kyleRhess/MicroMotor/uMotor_0p2/include/encoder.h

#ifndef ENCODER_H_ /* include guard */
#define ENCODER_H_

#include <stdio.h>

#include "stm32f4xx.h"
#include "system.h"

void Encoder_Init(void);
void Encoder_ZInit(void);
uint32_t Encoder_GetCounts(void);
double Encoder_GetAngle(void);
void Encoder_Reset(void);

extern uint32_t sens51[8];
extern uint32_t sens52[8];

#endif /* ENCODER_H_ */
