kyleRhess/MicroMotor/uMotor_0p2/src/adc.c

#include "adc.h"

ADC_HandleTypeDef hadc1;
DMA_HandleTypeDef hdma_adc1;

static uint32_t g_ADCValue1 = 0;
static float g_ADCValue2 	= 0;
static float g_ADCValue3 	= 0;
static float g_ADCValue4 	= 0;
static uint32_t g_ADCBuffer[ADC_BUF_LEN];

static float min_adc =  1.22f;
static float max_adc = 3.4f;
static float adcBias = 0;
static int adcBiasCount = 0;

void ADC_Init(void)
{
	ADC_ChannelConfTypeDef sConfig 		= {0};

	hadc1.Instance 						= ADC1;
	hadc1.Init.ClockPrescaler 			= ADC_CLOCK_SYNC_PCLK_DIV2;
	hadc1.Init.Resolution 				= ADC_RESOLUTION_12B;
	hadc1.Init.ScanConvMode 			= ENABLE;
	hadc1.Init.ContinuousConvMode 		= DISABLE;
	hadc1.Init.DiscontinuousConvMode 	= DISABLE;
	hadc1.Init.ExternalTrigConvEdge 	= ADC_EXTERNALTRIGCONVEDGE_NONE;
	hadc1.Init.ExternalTrigConv 		= ADC_SOFTWARE_START;
	hadc1.Init.DataAlign 				= ADC_DATAALIGN_RIGHT;
	hadc1.Init.NbrOfConversion 			= 4;
	hadc1.Init.DMAContinuousRequests 	= ENABLE;
	hadc1.Init.EOCSelection 			= ADC_EOC_SINGLE_CONV;

	if (HAL_ADC_Init(&hadc1) != HAL_OK)
	{
		Error_Handler();
	}

	sConfig.Channel 		= ADC_CHANNEL_2;
	sConfig.Rank 			= 1;
	sConfig.SamplingTime 	= ADC_SAMPLETIME_3CYCLES;
	if (HAL_ADC_ConfigChannel(&hadc1, &sConfig) != HAL_OK)
	{
		Error_Handler();
	}

	sConfig.Channel 		= ADC_CHANNEL_3;
	sConfig.Rank 			= 2;
	if (HAL_ADC_ConfigChannel(&hadc1, &sConfig) != HAL_OK)
	{
		Error_Handler();
	}

	sConfig.Channel 		= ADC_CHANNEL_15;
	sConfig.Rank 			= 3;
	if (HAL_ADC_ConfigChannel(&hadc1, &sConfig) != HAL_OK)
	{
		Error_Handler();
	}

	sConfig.Channel 		= ADC_CHANNEL_0;
	sConfig.Rank 			= 4;
	if (HAL_ADC_ConfigChannel(&hadc1, &sConfig) != HAL_OK)
	{
		Error_Handler();
	}

	HAL_ADC_Start_DMA(&hadc1, (uint32_t *)&g_ADCBuffer, ADC_BUF_LEN);
}

void HAL_ADC_ConvCpltCallback(ADC_HandleTypeDef* hadc)
{
//#define FILT_K		0.90f
#ifdef FILT_K
#define FILT_K_1	(1 - FILT_K)
	// Initial state needs to be set
	if(g_ADCValue1 == 0 && g_ADCValue2 == 0 && g_ADCValue3 == 0)
	{
		g_ADCValue1 	= g_ADCBuffer[2];
		g_ADCValue2 	= (float)g_ADCBuffer[0];
		g_ADCValue3 	= (float)g_ADCBuffer[1];
		g_ADCValue4 	= (float)g_ADCBuffer[3];
	}
	else
	{
		g_ADCValue1 	= g_ADCBuffer[2];
		g_ADCValue2 	= g_ADCValue2*FILT_K_1 + ((float)g_ADCBuffer[0])*FILT_K;
		g_ADCValue3 	= g_ADCValue3*FILT_K_1 + ((float)g_ADCBuffer[1])*FILT_K;
		g_ADCValue4 	= (float)g_ADCBuffer[3];
	}
#else
	g_ADCValue1 	= (float)g_ADCBuffer[2];
	g_ADCValue2 	= (float)g_ADCBuffer[0];
	g_ADCValue3 	= (float)g_ADCBuffer[1];
	g_ADCValue4 	= (float)g_ADCBuffer[3];
#endif

	m_fSupplyVolt 	= ((float)g_ADCValue1 * ADC_SCALE) / ADC_SUPPLY_DIV;
	m_fThrotVolt	= ((float)g_ADCValue4 * ADC_SCALE) / 0.5f;

	// Take out the throttle bias
	if(adcBiasCount == 9999)
		m_fThrotVolt -= adcBias;

	m_fCurrentA 	= ((((float)g_ADCValue3 * ADC_SCALE) - ADC_ZERO) * ADC_RES);
	m_fCurrentB 	= ((((float)g_ADCValue2 * ADC_SCALE) - ADC_ZERO) * ADC_RES);
	m_fCurrentC 	= -m_fCurrentA - m_fCurrentB;

	// EMRG stop if current gets too high
	if(m_fCurrentA > MAX_CURRENT || m_fCurrentA < -MAX_CURRENT ||
	   m_fCurrentB > MAX_CURRENT || m_fCurrentB < -MAX_CURRENT ||
	   m_fCurrentC > MAX_CURRENT || m_fCurrentC < -MAX_CURRENT)
	{
		Signal_SetMotorState(Signal_GetMotorState() | MOTOR_MODE_OVERCURRENT);
	}

	if(Clock_GetMs() > 1000)
	{
		if(m_fSupplyVolt < m_fSupplyVoltInit * 0.75f)
			Signal_SetMotorState(Signal_GetMotorState() | MOTOR_MODE_UNDERVOLT);
	}

	Run_SVM();
}


float ADC_GetThrottle(void)
{
	if(adcBiasCount < 1000)
	{
		adcBias += m_fThrotVolt;
		m_fSupplyVoltInit += m_fSupplyVolt;
		adcBiasCount++;
	}
	else if(adcBiasCount != 9999)
	{
		adcBias = adcBias / (float)adcBiasCount;
		m_fSupplyVoltInit = m_fSupplyVoltInit / (float)adcBiasCount;
		adcBiasCount = 9999;
	}

	if(m_fThrotVolt < min_adc)
		min_adc = m_fThrotVolt;
	else if(m_fThrotVolt > max_adc)
		max_adc = m_fThrotVolt;

	return System_mapVal(m_fThrotVolt, min_adc, max_adc, 0.0f, 100.0f);
}
