kyleRhess/MicroMotor/uMotor_0p2/include/pwm.h

#ifndef PWM_H_ /* include guard */
#define PWM_H_

#include <string.h>
#include <math.h>
#include "stm32f4xx_hal.h"
#include "stm32f4xx_hal_conf_template.h"
#include "stm32f4xx_hal_tim.h"
#include "stm32f4xx_hal_tim_ex.h"

#define DEAD_TIME				100		// ns
#define PWM_F					19738 	// Hz

#define CLOCK_CYCLES_PER_SECOND 100000000
#define PWM_PRESCALE			0
#define PWM_PERIOD			 	((CLOCK_CYCLES_PER_SECOND/2) / PWM_F) 		// Freq = 100000000 / ((PWM_PRESCALE + 1) * (PWM_PERIOD + 1))
#define PWM_FREQ 				(CLOCK_CYCLES_PER_SECOND / ((PWM_PRESCALE + 1) * (PWM_PERIOD + 1)))
#define PULSE_NS_PER_CNT		(10 * (PWM_PRESCALE+1))  					// = (10ns per Prescaler count) + 10ns
#define CNTS_FROM_US(xxx)		((xxx * 1000) / PULSE_NS_PER_CNT)
#define MAX_RELOAD              0xFFFF

typedef struct PWM_OUTPUT
{
	TIM_HandleTypeDef 	timer;
	float 				dutyCycle;
	uint32_t 			frequency;
	uint32_t 			Channel;
	TIM_TypeDef*		TIM;
} PWM_Out;

PWM_Out PWMtimer;

TIM_HandleTypeDef Initialize_PWM(PWM_Out * PWMType);
void PWM_adjust_DutyCycle(TIM_HandleTypeDef * pwmHandle, uint32_t Channel, float dutyCycle);
void PWM_adjust_PulseWidth(TIM_HandleTypeDef * pwmHandle, uint32_t Channel, float pulseWidth_us);
void PWM_adjust_Frequency(TIM_HandleTypeDef * pwmHandle, uint32_t Channel, uint32_t newFreq);
void HAL_TIM_PWM_MspInit(TIM_HandleTypeDef* htim_pwm);
void PWM_Set_Duty(TIM_HandleTypeDef * pwmHandle, uint32_t Channel, float dutyCycle);

#endif /* PWM_H_ */
